ElKinoflop/Vozvan/Case Files/Vozvan 2 - Accent.dxf

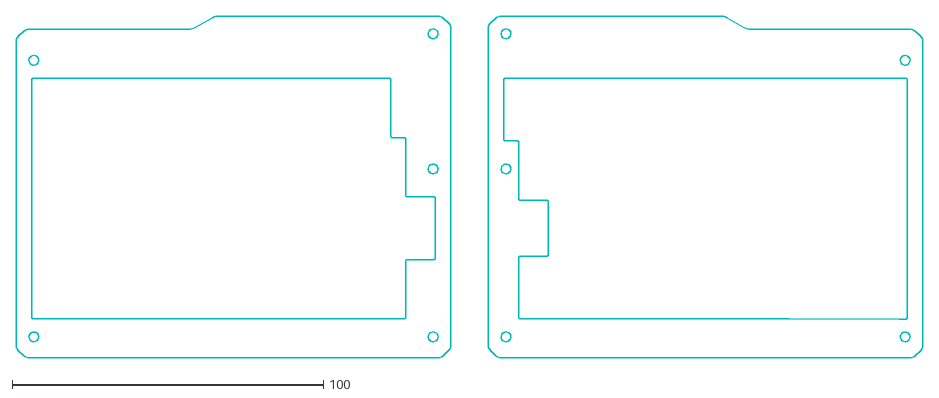
[picture p30: CAD file, 2025-01-11]
Case Files/Vozvan 2 - Accent.dxf
291.3 x 109.8
