ElKinoflop/Vozvan/Case Files/One Piece VFW/0VFWOP - Centre Cover.dxf

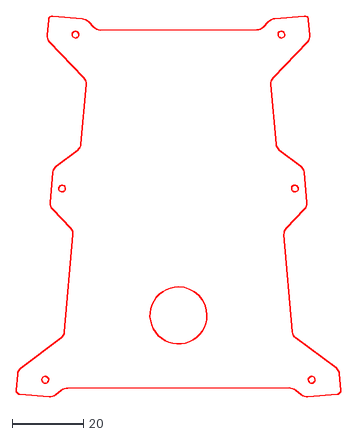
[picture p31: CAD file, 2025-01-25]
Case Files/One Piece VFW/0VFWOP - Centre Cover.dxf
91.3 x 107.0
