ElKinoflop/Vozvan/Case Files/Vozvan 3B - Plate Stabbed.dxf

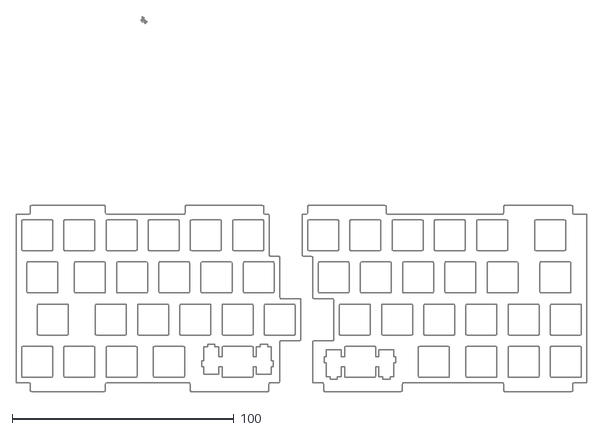
[picture p32: CAD file, 2025-01-11]
Case Files/Vozvan 3B - Plate Stabbed.dxf
257.7 x 169.5
