ElKinoflop/Vozvan/Case Files/One Piece VFW/5VFWOP - Mid Upper.dxf

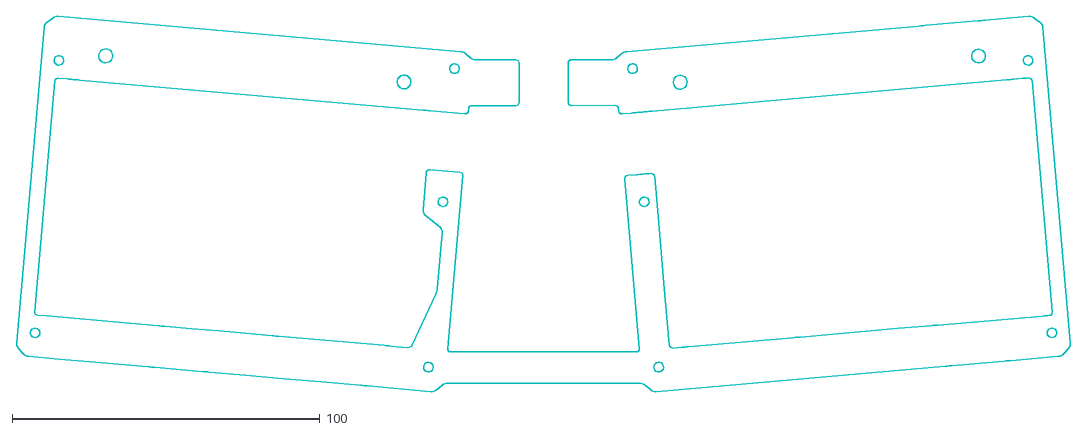
[picture p33: CAD file, 2025-01-25]
Case Files/One Piece VFW/5VFWOP - Mid Upper.dxf
342.4 x 122.0
