ElKinoflop/Vozvan/Case Files/Vozvan 5 - Mid Upper.dxf

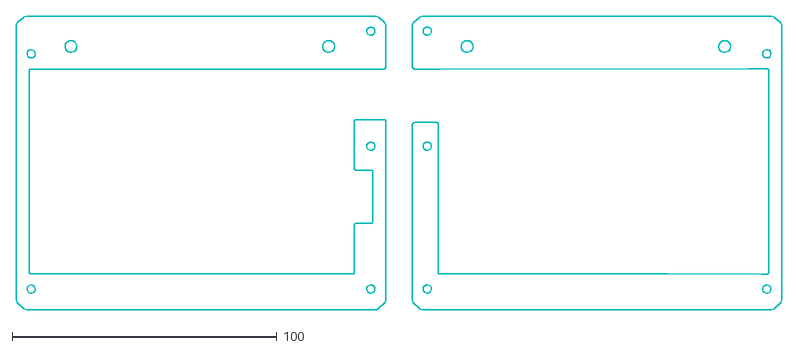
[picture p34: CAD file, 2025-01-11]
Case Files/Vozvan 5 - Mid Upper.dxf
289.2 x 110.9
