ElKinoflop/Vozvan/Case Files/One Piece VFW/7VFWOP - Mid Lower.dxf

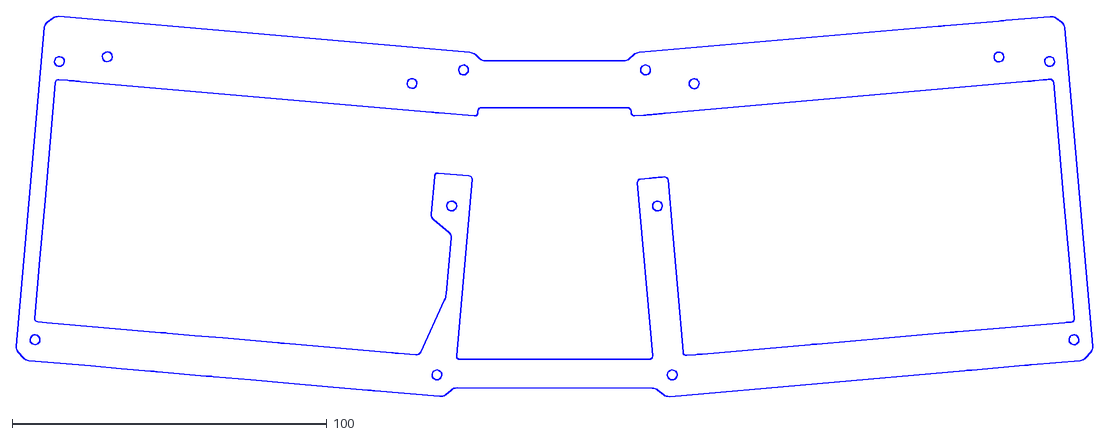
[picture p35: CAD file, 2025-01-25]
Case Files/One Piece VFW/7VFWOP - Mid Lower.dxf
342.2 x 120.9
