ElKinoflop/Vozvan/Case Files/Vozvan 4 - Plate Layer.dxf

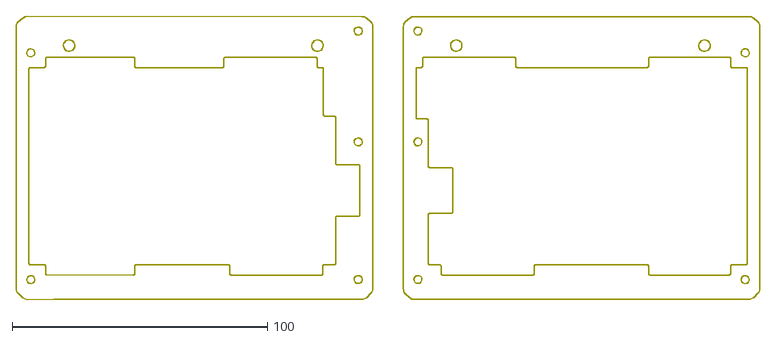
[picture p36: CAD file, 2025-01-11]
Case Files/Vozvan 4 - Plate Layer.dxf
291.3 x 110.9
