ElKinoflop/Vozvan/Case Files/One Piece VFW/6VFWOP - Mid Mid.dxf

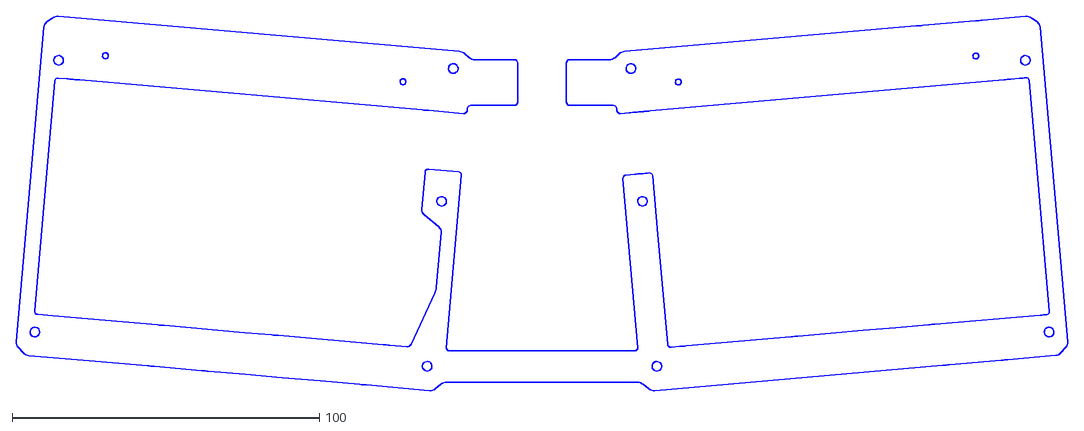
[picture p37: CAD file, 2025-01-25]
Case Files/One Piece VFW/6VFWOP - Mid Mid.dxf
342.4 x 122.0
