ElKinoflop/Vozvan/Case Files/Vozvan 9SEC-SFW - Feet x4.dxf

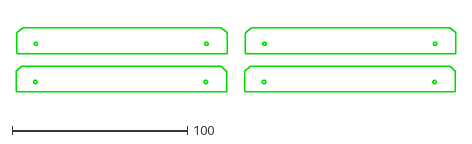
[picture p38: CAD file, 2025-01-11]
Case Files/Vozvan 9SEC-SFW - Feet x4.dxf
250.8 x 36.5
