ElKinoflop/Vozvan/Case Files/One Piece VFW/2VFWOP - Accent.dxf

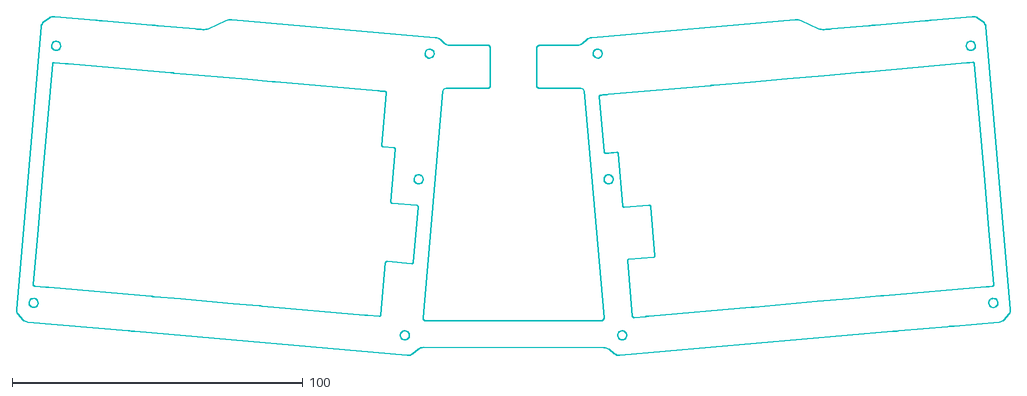
[picture p39: CAD file, 2025-01-25]
Case Files/One Piece VFW/2VFWOP - Accent.dxf
342.2 x 116.7
