ElKinoflop/Vozvan/Case Files/Vozvan 3 - Plate Stabless.dxf

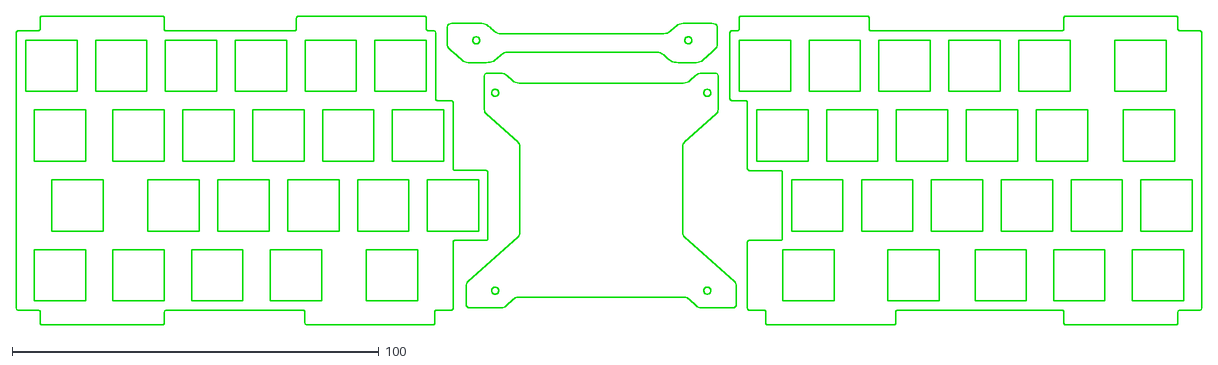
[picture p40: CAD file, 2025-01-11]
Case Files/Vozvan 3 - Plate Stabless.dxf
323.2 x 84.2
