ElKinoflop/Vozvan/Case Files/Vozvan 8VEC - Bottom.dxf

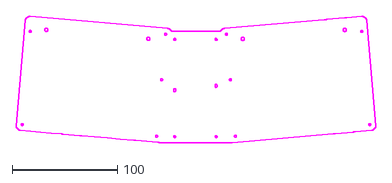
[picture p41: CAD file, 2025-01-11]
Case Files/Vozvan 8VEC - Bottom.dxf
342.0 x 120.1
