ElKinoflop/Vozvan/Case Files/Vozvan 1 - Top.dxf

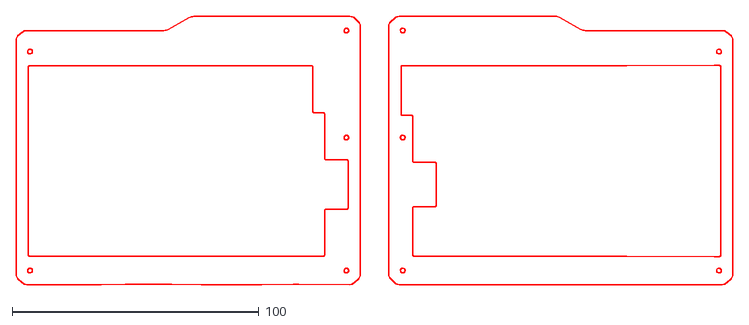
[picture p42: CAD file, 2025-01-11]
Case Files/Vozvan 1 - Top.dxf
290.8 x 108.7
