ElKinoflop/Vozvan/Case Files/Vozvan 7 - Mid Lower.dxf

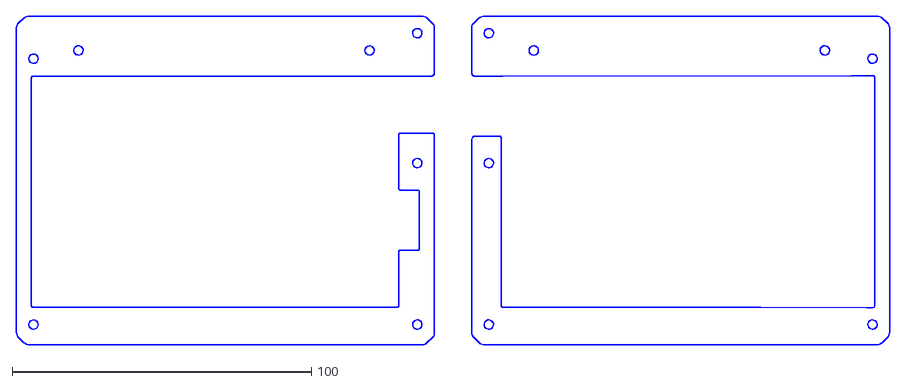
[picture p43: CAD file, 2025-01-11]
Case Files/Vozvan 7 - Mid Lower.dxf
291.8 x 109.8
