ElKinoflop/Vozvan/Case Files/Vozvan 9VEC-VFW - Feet x4.dxf

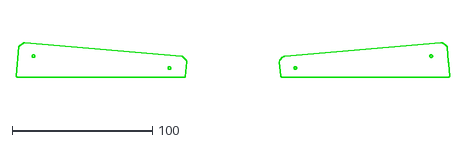
[picture p44: CAD file, 2025-01-11]
Case Files/Vozvan 9VEC-VFW - Feet x4.dxf
309.0 x 24.8
