ElKinoflop/Vozvan/Case Files/Vozvan 6 - Mid Mid.dxf

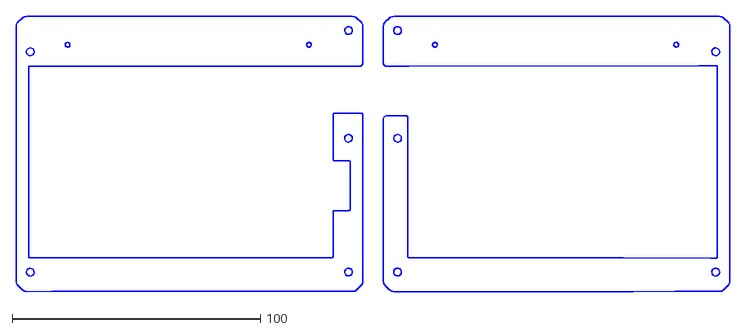
[picture p45: CAD file, 2025-01-11]
Case Files/Vozvan 6 - Mid Mid.dxf
287.6 x 110.9
